demultiplexer/fancontroller/Gerber files/FreePCB output format and renders/board_outline.png

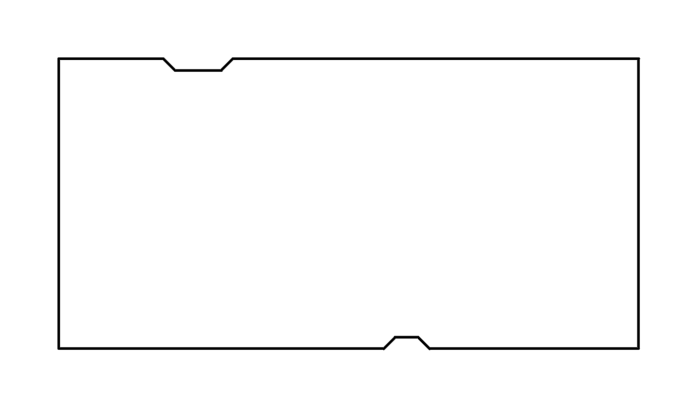
Gerber files/FreePCB output format and renders/board_outline.png
