demultiplexer/fancontroller/Gerber files/FreePCB output format and renders/bottom_copper.png

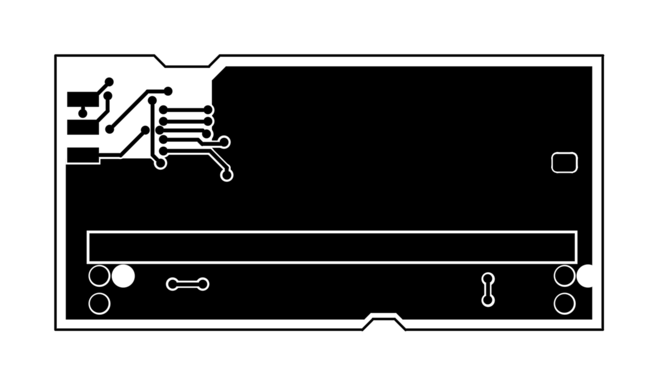
Gerber files/FreePCB output format and renders/bottom_copper.png
