demultiplexer/fancontroller/Gerber files/FreePCB output format and renders/bottom_paste_mask.png

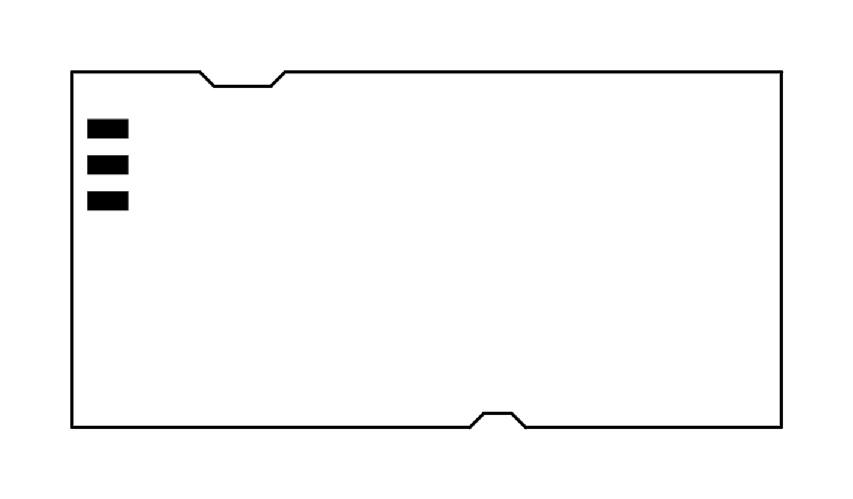
Gerber files/FreePCB output format and renders/bottom_paste_mask.png
