demultiplexer/fancontroller/Gerber files/FreePCB output format and renders/top_copper.png

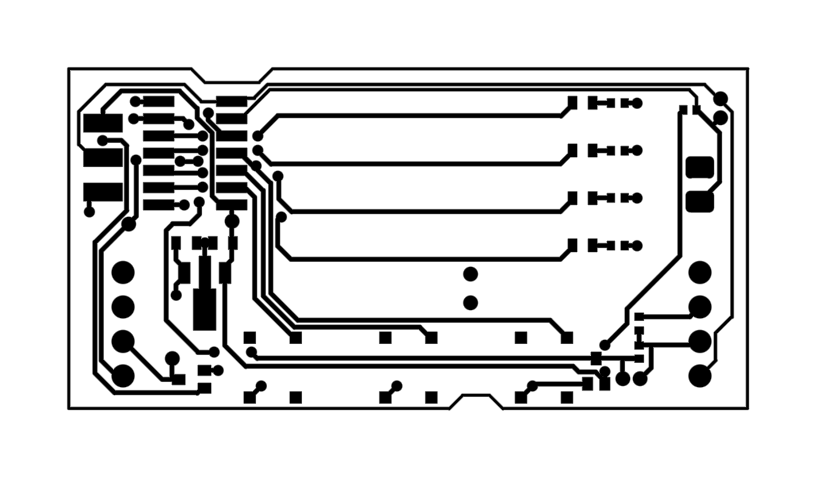
Gerber files/FreePCB output format and renders/top_copper.png
