demultiplexer/fancontroller/Gerber files/FreePCB output format and renders/top_paste_mask.png

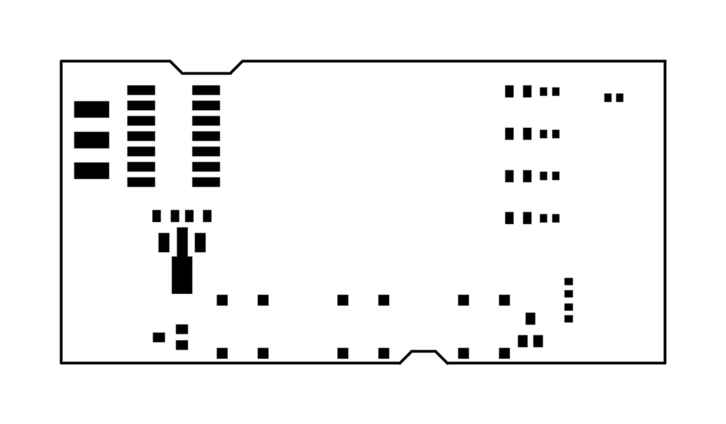
Gerber files/FreePCB output format and renders/top_paste_mask.png
