demultiplexer/fancontroller/Gerber files/FreePCB output format and renders/top_silk.png

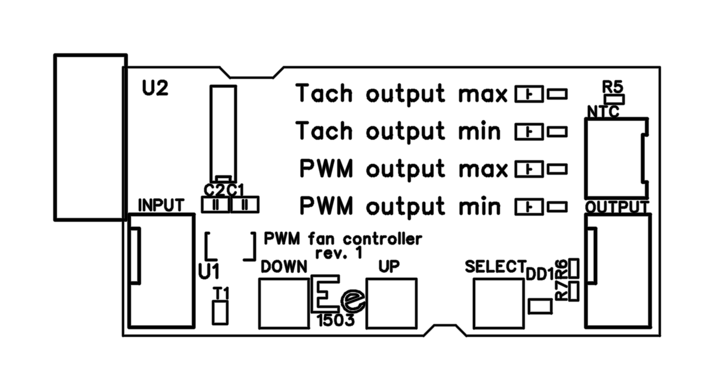
Gerber files/FreePCB output format and renders/top_silk.png
