demultiplexer/fancontroller/Gerber files/FreePCB output format and renders/bottom_solder_mask.png

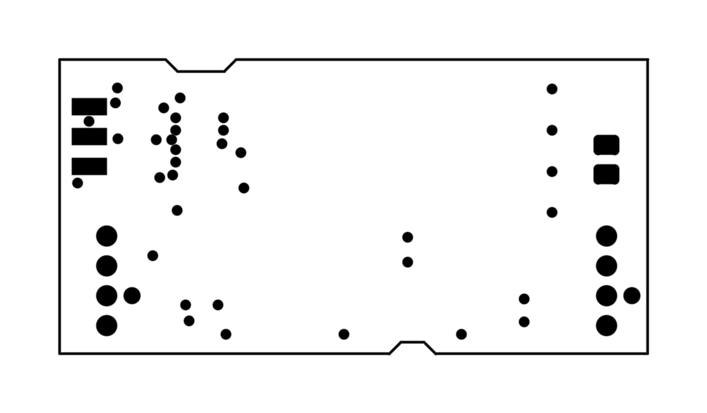
Gerber files/FreePCB output format and renders/bottom_solder_mask.png
