demultiplexer/fancontroller/Gerber files/FreePCB output format and renders/top_solder_mask.png

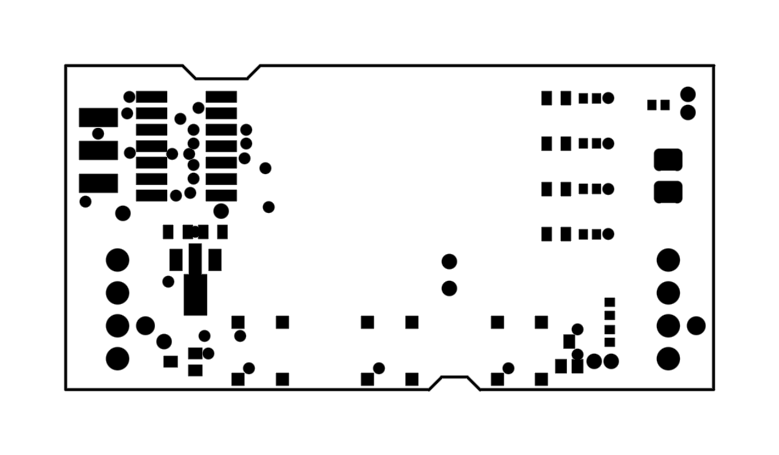
Gerber files/FreePCB output format and renders/top_solder_mask.png
