demultiplexer/fancontroller/firmware-measurementcycle.png

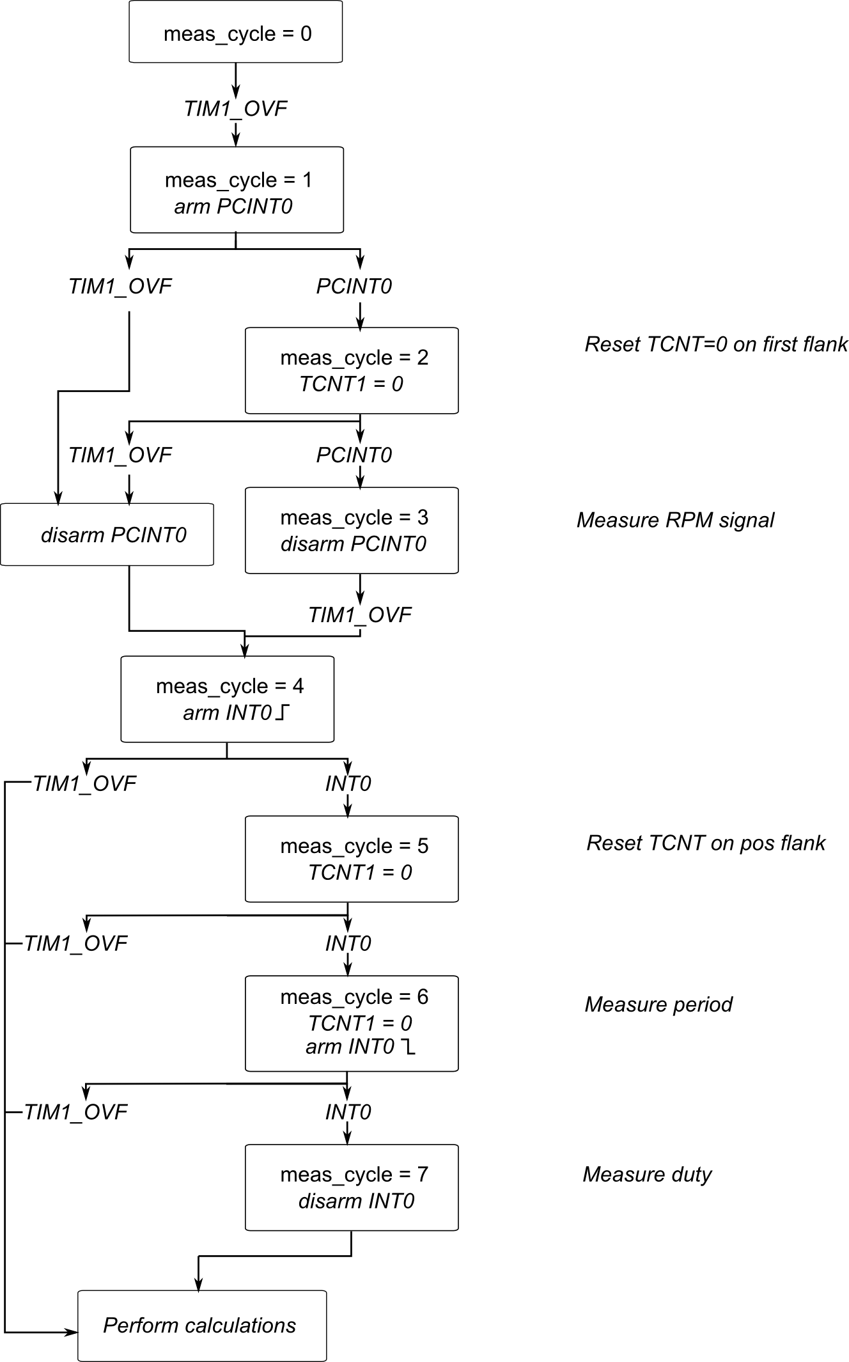
firmware-measurementcycle.png
